rschenk/cfx_chicago_stenographer/stl/single_keys/cs_r3_175.stl

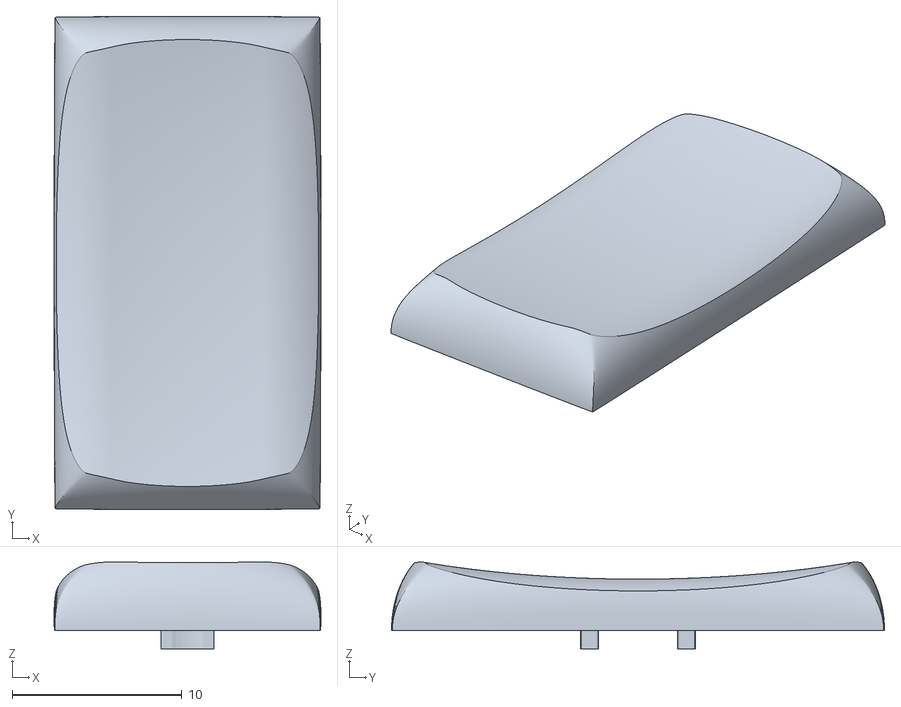
[picture p13: CAD file, 2024-02-03]
stl/single_keys/cs_r3_175.stl
15.7 x 29.0 x 5.12
