rschenk/cfx_chicago_stenographer/stl/single_keys/cs_r4x_1.stl

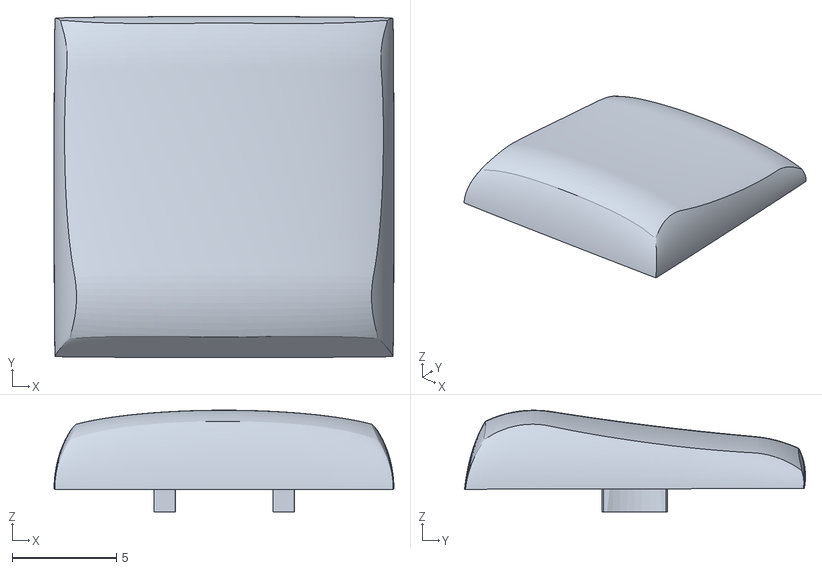
[picture p14: CAD file, 2024-02-03]
stl/single_keys/cs_r4x_1.stl
16.3 x 16.4 x 4.88
