rschenk/cfx_chicago_stenographer/stl/single_keys/cs_r3_125_bar.stl

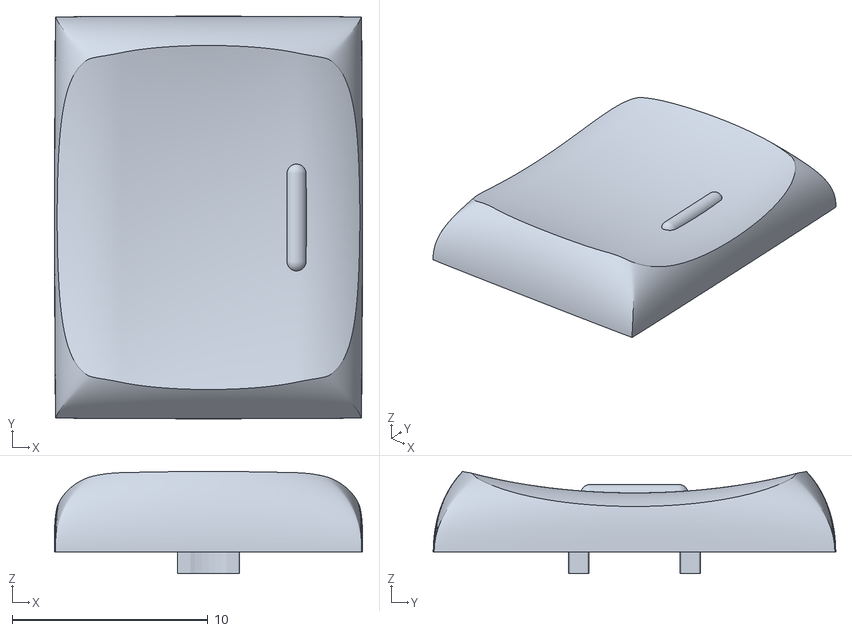
[picture p15: CAD file, 2024-02-03]
stl/single_keys/cs_r3_125_bar.stl
15.7 x 20.5 x 5.21
