rschenk/cfx_chicago_stenographer/stl/single_keys/cs_r3_225.stl

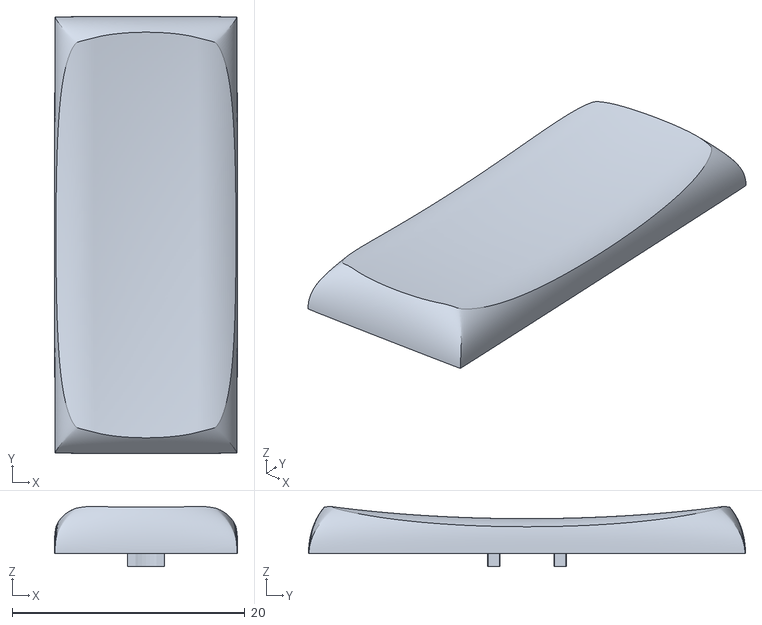
[picture p16: CAD file, 2024-02-03]
stl/single_keys/cs_r3_225.stl
15.7 x 37.5 x 5.16
