rschenk/cfx_chicago_stenographer/stl/single_keys/cs_r3_125.stl

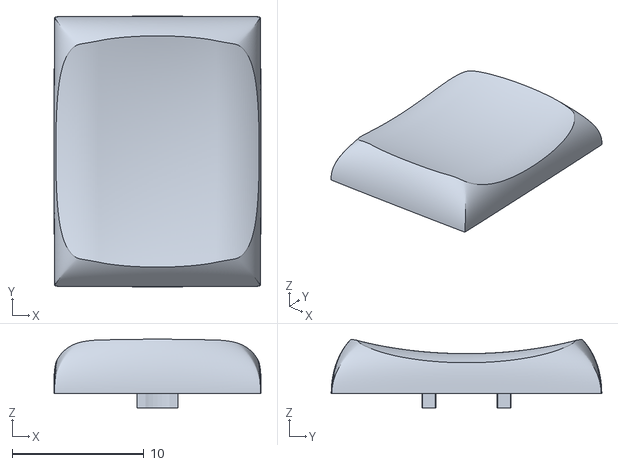
[picture p17: CAD file, 2024-02-03]
stl/single_keys/cs_r3_125.stl
15.7 x 20.5 x 5.21
