rschenk/cfx_chicago_stenographer/stl/single_keys/cs_r3_1_bar.stl

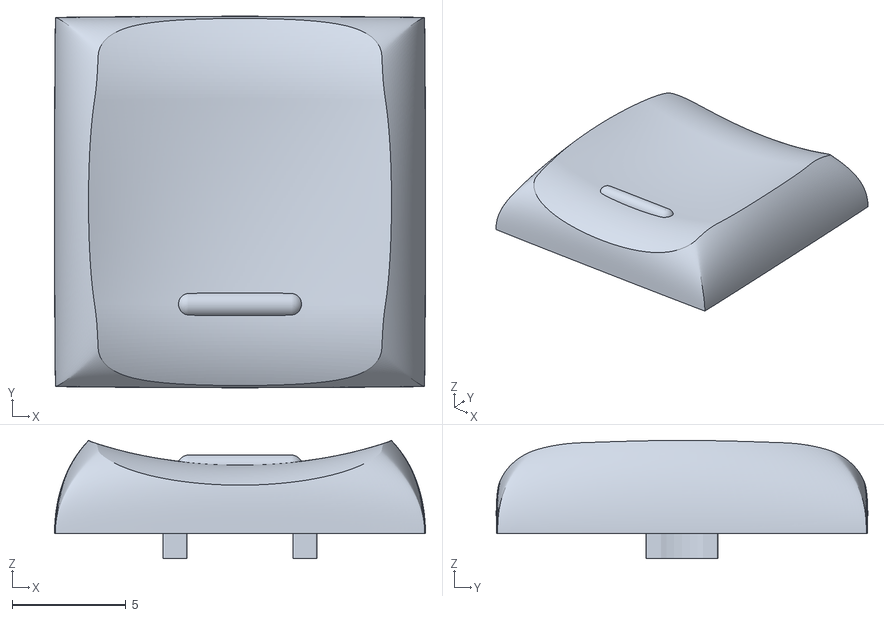
[picture p18: CAD file, 2024-02-03]
stl/single_keys/cs_r3_1_bar.stl
16.3 x 16.3 x 5.19
