rschenk/cfx_chicago_stenographer/stl/single_keys/cs_r3x_1.stl

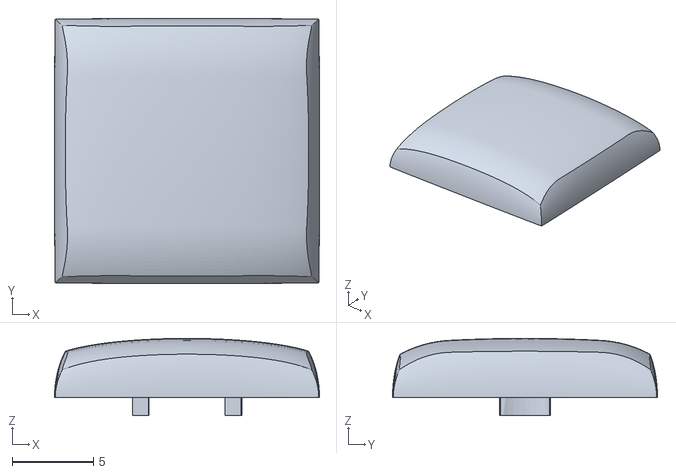
[picture p19: CAD file, 2024-02-03]
stl/single_keys/cs_r3x_1.stl
16.3 x 16.3 x 4.75
